ompatil115/Centralized-Robotic-Systems-Project/devices/Robot-Car-V1/docs/media/Car_V1.kicad_sch

## KiCad design devices/Robot-Car-V1/docs/media/Car_V1.kicad_sch (2026-10-02)

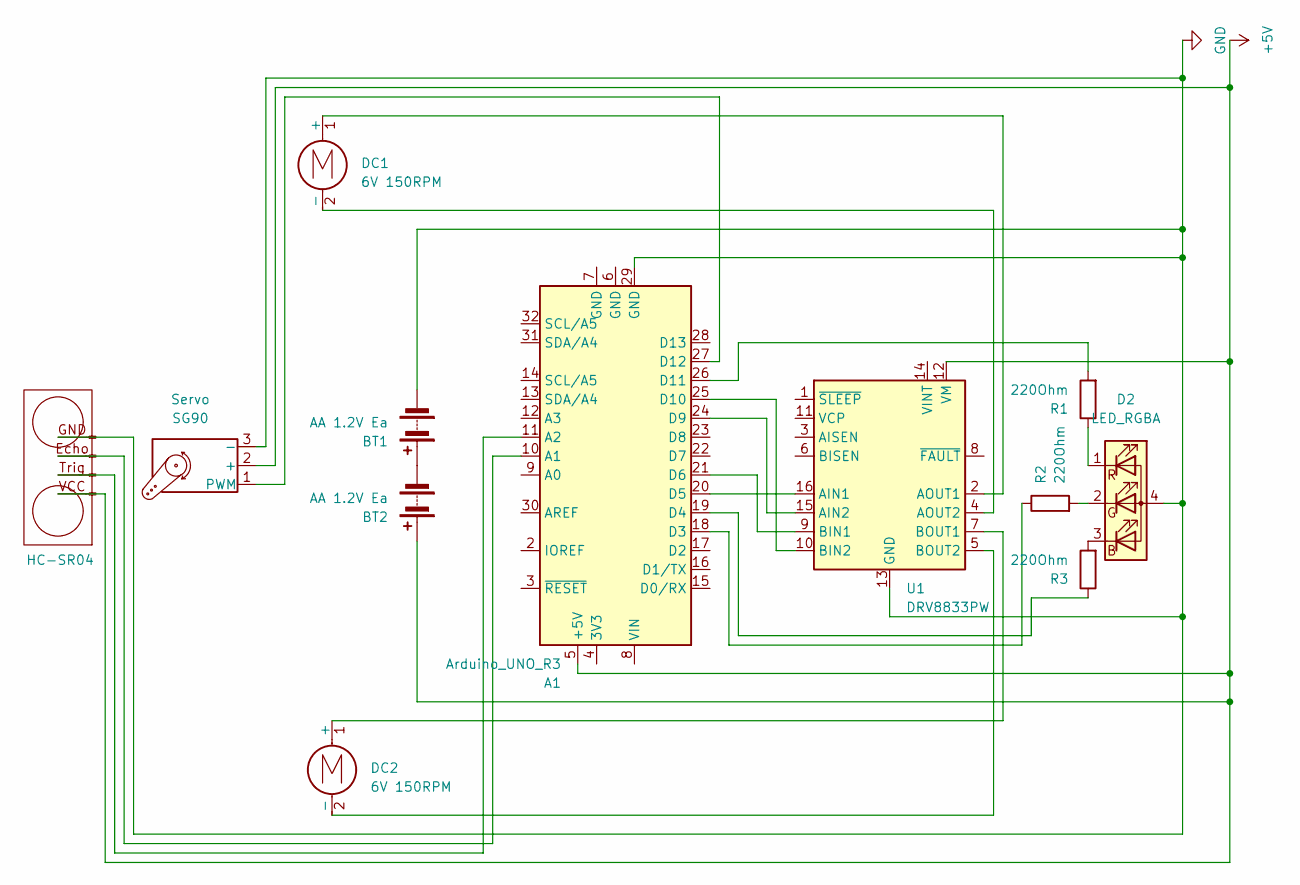
[picture p3: schematic Car_V1.kicad_sch]

Parts:
A1: Arduino_UNO_R3
BT1, BT2: AA 1.2V Ea; QFN-40-1EP_6x6mm_P0.5mm_EP4.6x4.6mm
D2: LED_RGBA
DC1, DC2: 6V 150RPM; TSSOP-16_4.4x5mm_P0.65mm
HC-SR04: Transformer_Wuerth_750343373
R1, R2, R3: 220Ohm; DIP-8_W7.62mm
Servo: SG90; WSON-8-1EP_6x5mm_P1.27mm_EP3.4x4mm
U1: DRV8833PW; TSSOP-16_4.4x5mm_P0.65mm

Connections:
+5V: A1.5 (+5V), BT2.1 (+), HC-SR04.VCC, Servo.2 (+), U1.12 (VM)
GND: A1.29 (GND), BT1.2 (-), D2.4 (A), HC-SR04.GND, Servo.3 (-), U1.13 (GND)
unnamed: A1.10 (A1), HC-SR04.Echo
unnamed: A1.11 (A2), HC-SR04.Trig
unnamed: A1.18 (D3), R2.1
unnamed: A1.19 (D4), R3.1
unnamed: A1.20 (D5), U1.16 (AIN1)
unnamed: A1.21 (D6), U1.9 (BIN1)
unnamed: A1.24 (D9), U1.15 (AIN2)
unnamed: A1.25 (D10), U1.10 (BIN2)
unnamed: A1.26 (D11), R1.2
unnamed: A1.27 (D12), Servo.1 (PWM)
unnamed: BT1.1 (+), BT2.2 (-)
unnamed: D2.1 (RK), R1.1
unnamed: D2.2 (GK), R2.2
unnamed: D2.3 (BK), R3.2
unnamed: DC1.1 (+), U1.2 (AOUT1)
unnamed: DC1.2 (-), U1.4 (AOUT2)
unnamed: DC2.1 (+), U1.7 (BOUT1)
unnamed: DC2.2 (-), U1.5 (BOUT2)
